dzielislaw/home_weather_station/Core/Inc/RGB565.h

//
// Created by HP on 29.03.2024.
//

#ifndef STACJA_POGODOWA_RGB565_FOR_ST7735S_H
#define STACJA_POGODOWA_RGB565_FOR_ST7735S_H

#define ALICEBLUE 0xEFBF
#define ANTIQUEWHITE 0xF75A
#define AQUAMARINE 0x7FFA
#define AZURE 0xEFFF
#define BEIGE 0XF7BB
#define BISQUE 0xFF18
#define BLACK 0x0000
#define BLANCHEDALMOND 0xFF59
#define BLUE 0x001F
#define BLUEVIOLET 0x897B
#define BROWN 0xA145
#define BURLYWOOD 0xDDB0
#define CADETBLUE 0x64F3
#define CHARTREUSE 0x7FE0
#define CHOCOLATE 0xD344
#define CORAL 0xFBEA
#define CORNFLOWERBLUE 0x64BD
#define CORNSILK 0xFFBB
#define CRIMSON 0xD8A7
#define CYAN 0x07FF
#define DARKBLUE 0x0011
#define DARKCYAN 0x0451;
#define DARKGOLDENROD 0xB421
#define DARKGRAY 0xAD55
#define DARKGREEN 0x0320
#define DARKGREY 0xAD55
#define DARKKHAKI 0xBDAD
#define DARKMAGENTA 0x8811
#define DARKOLIVEGREEN 0x5346
#define DARKORANGE 0xFC60
#define DARKORCHID 0x9999
#define DARKRED 0x8800
#define DARKSALMON 0xE4AF
#define DARKSEAGREEN 0x8DD1
#define DARKSLATEBLUE 0x49F1
#define DARKSLATEGREY 0x328A
#define GREEN 0x0400
#define KHAKI 0xEF31
#define MAGENTA 0xF81F
#define RED 0xF800
#define SNOW 0xFFDE
#define SPRINGGREEN 0x07EF
#define STEELBLUE 0x4C16
#define TAN 0xD591
#define TEAL 0x0410
#define WHITE 0xFFFF

#endif //STACJA_POGODOWA_RGB565_FOR_ST7735S_H
